jakubfi/ictester/fw/serial.c

//  Copyright (c) 2013 Jakub Filipowicz <jakubf@gmail.com>
//
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
#include <stddef.h>
#include <inttypes.h>
#include <avr/io.h>

#include "serial.h"

// -----------------------------------------------------------------------
void serial_init(unsigned long baud)
{
	UCSR0A = 1 << U2X0;
	uint16_t speed = F_CPU / 8 / baud-1;
	UBRR0H = speed >> 8;
	UBRR0L = speed;
	UCSR0B = (1 << TXEN0) | (1 << RXEN0);
	UCSR0C = (1 << UCSZ01) | (1 << UCSZ00); // 8N1
}

// -----------------------------------------------------------------------
void serial_tx_char(uint8_t c)
{
	while (!(UCSR0A & (1 << UDRE0)));
	UDR0 = c;
}

// -----------------------------------------------------------------------
uint8_t serial_rx_char()
{
	while (!(UCSR0A & (1 << RXC0)));
	return UDR0;
}

// -----------------------------------------------------------------------
uint16_t serial_rx_16le()
{
	uint16_t tmp = serial_rx_char();
	tmp |= (uint16_t) serial_rx_char() << 8;
	return tmp;
}

// -----------------------------------------------------------------------
void serial_tx_16le(uint16_t v)
{
	serial_tx_char(v & 0xff);
	serial_tx_char(v >> 8);
}

// -----------------------------------------------------------------------
void serial_rx_bytes(uint8_t *data, uint16_t count)
{
	while (count) {
		*data = serial_rx_char();
		data++;
		count--;
	}
}

// -----------------------------------------------------------------------
void serial_tx_bytes(uint8_t *data, uint16_t count)
{
	while (count--) {
		serial_tx_char(*(data++));
	}
}

// vim: tabstop=4 shiftwidth=4 autoindent
